alanmimms/NexRx/hw/DFM-fail.md

[C2862740, C133940, C133940, C133940, C133940, C133940, C1710,
C133940, C133940, C50254, C133940, C50254, C1710, C50254, C96446,
C1710, C913830, C1974049, C96446, C2862740, C96446, C96446, C96446,
C96446, C96446, C96446, C96446, C96446, C96446, C96446, C96446,
C76991, C96446, C96446, C96446, C96446, C96446, C96446, C96446,
C76991, C96446, C96446, C96446, C96446, C96446, C96446, C96446,
C96446, C52259879, C96446, C96446, C76991, C76991, C96446, C96446,
C96446, C52259879, C96446, C96446, C96446, C96446, C96446, C96446,
C96446, C96446, C96446, C96446, C96446, C96446, C96446, C96446,
C96446, C96446, C96446, C96446, C96446, C96446, C96446, C96446,
C96446] Pls replace the problem compoments to proceed as checked.
Please edit in 1427:54:8 hours, or else the order will be cancelled
automatically

As shown below, seems the packages of the parts ( U1501、U1504、
C133940, C1516、C1515、C1513、C1512、C219、C918、C1514、D101、C1517、
C1502、C1507、C1506、C207、C1006、C1004、C909、C1206、C911、C902、
C1005、C1511、C1009、C904、C208、C1003、C107、C1205、C108、C1008、
C1007、C1202、C922、C1201、C1204、C1203、C212、C937、C231、C228、C1501、
C903、C1404、C1406、C1409、C229、C218、C822、C943、C232、C1405、C1408、
C837、C944、C213、C1407、C1403、C227、C809、C844、C843、C230、C233、
C803、C811、C802、C804、C818、L304、L303、D201) cannot match the
corresponding footprint on the PCB board.

x C1003
x C1004
x C1005
x C1006
x C1007
x C1008
x C1009
x C108
x C1201
x C1202
x C1203
x C1204
x C1205
x C1206
x C1403
x C1404
x C1405
x C1406
x C1407
x C1408
x C1409
x C1501
x C1502
x C1506
x C1507
x C1511
x C1514
x C1517
x C207
x C208
x C212
x C213
x C218
x C227
x C228
x C229
x C230
x C231
x C232
x C233
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
