alanmimms/NexRx/CPLD/top.sv

import CPLDRegs::*;

/**
 * nexrx-top.sv
 * Top-level module for NexRx CPLDs.
 */
module top (
	    input  logic clkTCXO,	// External TCXO
	    input  logic clkSynth,	// Si5351 generated "VFO" for phase outputs

	    /* SPI Slave Interface */
	    input  logic spiSCK,
	    input  logic spiMOSI,
	    output logic spiMISO,
	    input  logic spiNSS,

	    input  logic gnssPPS,	// GNSS 1pps signal for TCXO freq counter

	    // Output for each octature phase
	    output logic [7:0] nPh
	    );

  timeunit 1ns;
  timeprecision 1ps;

  /* Clocking & Reset */
  logic clkSys;    // TCXO based Master Clock
  logic clkVFO;	   // Current "VFO" freq clock
  logic resetN;

  // THIS PROBABLY NEEDS GLOBAL CLOCK BUFFER.
  assign clkSys = clkTCXO;
  assign clkVFO = clkSynth;

  initial resetN = 1;
  initial control = initCPLDControl;

  //==================================================================
  // Register Bank & SPI
  //==================================================================
  tCPLDControl control;
  logic [63:0] tcxoValue;

  logic [31:0] shiftReg;
  logic [5:0]  bitCnt;
  logic [7:0]  cmdLatch;
  logic        cmdDone;

  logic [6:0]  addr;
  logic        isWrite;
  logic [31:0] dataIn;
  logic [31:0] dataOut;

  //==================================================================
  // SPI Frontend
  //==================================================================
  always_ff @(posedge spiSCK or posedge spiNSS) begin

    if (spiNSS) begin
      bitCnt <= 6'd0;
      cmdDone <= 1'b0;
      cmdLatch <= 8'h0;
    end else begin

      if (bitCnt < 6'd8) begin
        cmdLatch <= {cmdLatch[6:0], spiMOSI};
      end else begin
        shiftReg <= {shiftReg[30:0], spiMOSI};
      end

      if (bitCnt == 6'd39) begin
        cmdDone <= 1'b1;
      end else begin
        bitCnt <= bitCnt + 1'b1;
      end
    end
  end

  always_ff @(negedge spiSCK or posedge spiNSS) begin

    if (spiNSS) begin
      spiMISO <= 1'b0;
    end else begin

      if (bitCnt >= 6'd8 && bitCnt < 6'd40) begin
        spiMISO <= dataOut[39 - bitCnt];
      end else begin
        spiMISO <= 1'b0;
      end
    end
  end

  assign addr = cmdLatch[6:0];
  assign isWrite = cmdLatch[7];
  assign dataIn = shiftReg;

  //==================================================================
  // Register Logic
  //==================================================================
  always_ff @(posedge clkSys) begin

    if (cmdDone) begin

      if (isWrite) begin

        case (addr)
	  aCPLDControl:	control <= dataIn;
	  default: ;
        endcase
      end
    end
  end

  always_comb begin
    case (addr)
      aCPLDControl:	dataOut = 32'(control);
      aCPLDPPSLatchHi:	dataOut = tcxoValue[63:32];
      aCPLDPPSLatchLo:	dataOut = tcxoValue[31:0];
      aCPLDSig:		dataOut = eSigValVal;	/* 'NxRx' */
      default:		dataOut = 'hDEADBEEF;
    endcase
  end

  //==================================================================
  // Precision frequency counter for clkSys gated by 1pps from GNSS.
  //==================================================================
  logic [63:0] tcxoCounter;
  initial tcxoCounter = 0;

  // Synchronizer to bring 1pps signal into TCXO clock domain safely.
  logic [2:0] ppsSync;
  wire ppsRise = ppsSync[1] & ~ppsSync[2];

  always_ff @(posedge clkSys) begin
    ppsSync <= {ppsSync[1:0], gnssPPS};
  end

  always_ff @(posedge clkSys) begin
    tcxoCounter <= tcxoCounter + 1'b1;

    if (ppsRise) begin
      tcxoValue <= tcxoCounter;
    end
  end

  //==================================================================
  // Phase Generators (Walking Rings)
  //==================================================================
  logic [7:0] osdPhases;

  initial osdPhases = 8'b10000000;

  always_ff @(negedge clkVFO) begin

    if (control.octMode)
      nPh <= ~osdPhases;
    else
      nPh <= ~{'0, osdPhases[6], '0, osdPhases[4], '0, osdPhases[2], '0, osdPhases[0]};

    osdPhases <= {osdPhases[6:0], osdPhases[7]};
  end

endmodule
