alanmimms/NexRx/app/src/TwinConn.cpp

#include "TwinConn.hpp"
#include <cbor.h>
#include <iostream>
#include <cmath>

namespace nexrx {

TwinConn::~TwinConn() {
  shutdown();
}

bool TwinConn::initialize(const TwinConfig& cfg) {
  if (connected) {
    return true;
  }
  config = cfg;
  frameBuffer.reserve(cfg.frameBufferSize);

  TCPControlClientConfig controlConfig;
  controlConfig.host = cfg.host;
  controlConfig.port = cfg.controlPort;
  control = std::make_unique<TCPControlClient>(controlConfig);
  if (!control->connect()) {
    return false;
  }

  UDPStreamClientConfig streamConfig;
  streamConfig.port = cfg.streamPort;
  streamConfig.receiveBufferSize = cfg.receiveBufferSize;
  stream = std::make_unique<UDPStreamClient>(streamConfig);
  if (!stream->connect()) {
    return false;
  }

  connected = true;
  return true;
}

void TwinConn::shutdown() {
  stopReceiving();
  if (control && connected) {
    uint8_t buf[64];
    CborEncoder enc, arr;
    cbor_encoder_init(&enc, buf, sizeof(buf), 0);
    cbor_encoder_create_array(&enc, &arr, 1);
    cbor_encode_uint(&arr, Control::CMD_GBYE);
    cbor_encoder_close_container(&enc, &arr);
    sendCBORRequest(Control::CMD_GBYE, {buf, buf + cbor_encoder_get_buffer_size(&enc, buf)});
    control->disconnect();
  }
  if (stream) {
    stream->disconnect();
  }
  connected = false;
}

bool TwinConn::startReceiving() {
  if (!connected) {
    return false;
  }
  if (receiving) {
    return true;
  }
  stopRequested = false;
  receiving = true;
  receiveThread = std::thread(&TwinConn::receiveLoop, this);
  return true;
}

void TwinConn::stopReceiving() {
  if (!receiving) {
    return;
  }
  stopRequested = true;
  if (receiveThread.joinable()) {
    receiveThread.join();
  }
  receiving = false;
}

size_t TwinConn::pollFrames(size_t maxFrames) {
  if (!connected || !stream) {
    return 0;
  }
  frameBuffer.clear();
  size_t count = 0;
  while (count < maxFrames) {
    auto res = stream->read(std::chrono::milliseconds(0));
    if (!res.ok()) {
      break;
    }
    
    IQFrame frame = res.value;
    lastSequenceReceived = frame.sequence;
    lastFrameReceived = frame;
    ++framesReceivedCount;
    ++count;
    frameBuffer.push_back(frame);
  }

  if (count > 0) {
    std::lock_guard<std::mutex> lock(callbackMutex);
    if (frameCallback) {
      for (const auto& frame : frameBuffer) {
        frameCallback(frame);
      }
    }
    if (batchCallback) {
      batchCallback(frameBuffer);
    }
  }
  return count;
}

void TwinConn::receiveLoop() {
  while (!stopRequested) {
    if (pollFrames(2048) == 0) {
      std::this_thread::sleep_for(std::chrono::microseconds(100));
    }
  }
}

void TwinConn::pollStateAsync() {
  uint8_t buf[64];
  CborEncoder enc, arr;
  cbor_encoder_init(&enc, buf, sizeof(buf), 0);
  cbor_encoder_create_array(&enc, &arr, 1);
  cbor_encode_uint(&arr, Control::CMD_GET_STATE);
  cbor_encoder_close_container(&enc, &arr);
  
  auto resp = sendCBORRequest(Control::CMD_GET_STATE, {buf, buf + cbor_encoder_get_buffer_size(&enc, buf)});
  if (!resp.empty()) {
      std::lock_guard<std::mutex> lock(stateMutex);
      cachedStateCBOR = resp;
  }
}

std::vector<uint8_t> TwinConn::processResponse(const std::vector<uint8_t>& data, uint32_t cmdId) {
  (void)cmdId;
  if (data.empty()) {
    return {};
  }
  CborParser parser;
  CborValue it, array;
  if (cbor_parser_init(data.data(), data.size(), 0, &parser, &it) != CborNoError) {
    return {};
  }
  cbor_value_enter_container(&it, &array);
  int64_t status;
  cbor_value_get_int64(&array, &status);
  if (status != 0) {
    return {};
  }
  return data;
}

std::vector<uint8_t> TwinConn::sendCBORRequest(uint32_t cmdId, const std::vector<uint8_t>& request) {
  std::lock_guard<std::mutex> lock(controlMutex);
  auto res = control->sendRequest(request, std::chrono::milliseconds(500));
  if (!res.ok()) {
    return {};
  }
  return processResponse(res.value, cmdId);
}

bool TwinConn::setVFO(double freqHz, double offsetHz) {
  uint8_t buf[128];
  CborEncoder enc, arr;
  cbor_encoder_init(&enc, buf, sizeof(buf), 0);
  cbor_encoder_create_array(&enc, &arr, 3);
  cbor_encode_uint(&arr, Control::CMD_SET_VFO);
  cbor_encode_double(&arr, freqHz);
  cbor_encode_double(&arr, offsetHz);
  cbor_encoder_close_container(&enc, &arr);
  return !sendCBORRequest(Control::CMD_SET_VFO, {buf, buf + cbor_encoder_get_buffer_size(&enc, buf)}).empty();
}

bool TwinConn::setAtten(int dbValue) {
  uint8_t buf[128];
  CborEncoder enc, arr;
  cbor_encoder_init(&enc, buf, sizeof(buf), 0);
  cbor_encoder_create_array(&enc, &arr, 2);
  cbor_encode_uint(&arr, Control::CMD_SET_ATTEN);
  cbor_encode_int(&arr, dbValue);
  cbor_encoder_close_container(&enc, &arr);
  return !sendCBORRequest(Control::CMD_SET_ATTEN, {buf, buf + cbor_encoder_get_buffer_size(&enc, buf)}).empty();
}

bool TwinConn::setPGAGain(int code) {
  uint8_t buf[128];
  CborEncoder enc, arr;
  cbor_encoder_init(&enc, buf, sizeof(buf), 0);
  cbor_encoder_create_array(&enc, &arr, 2);
  cbor_encode_uint(&arr, Control::CMD_SET_PGA_GAIN);
  cbor_encode_int(&arr, code);
  cbor_encoder_close_container(&enc, &arr);
  return !sendCBORRequest(Control::CMD_SET_PGA_GAIN, {buf, buf + cbor_encoder_get_buffer_size(&enc, buf)}).empty();
}

bool TwinConn::setAGCMode(int mode) {
  uint8_t buf[128];
  CborEncoder enc, arr;
  cbor_encoder_init(&enc, buf, sizeof(buf), 0);
  cbor_encoder_create_array(&enc, &arr, 2);
  cbor_encode_uint(&arr, Control::CMD_SET_AGC_MODE);
  cbor_encode_int(&arr, mode);
  cbor_encoder_close_container(&enc, &arr);
  return !sendCBORRequest(Control::CMD_SET_AGC_MODE, {buf, buf + cbor_encoder_get_buffer_size(&enc, buf)}).empty();
}

bool TwinConn::setISGFreq(double freqHz) {
  uint8_t buf[128];
  CborEncoder enc, arr;
  cbor_encoder_init(&enc, buf, sizeof(buf), 0);
  cbor_encoder_create_array(&enc, &arr, 2);
  cbor_encode_uint(&arr, Control::CMD_SET_ISG_FREQ);
  cbor_encode_double(&arr, freqHz);
  cbor_encoder_close_container(&enc, &arr);
  return !sendCBORRequest(Control::CMD_SET_ISG_FREQ, {buf, buf + cbor_encoder_get_buffer_size(&enc, buf)}).empty();
}

bool TwinConn::setISGEnable(bool enabled) {
  uint8_t buf[64];
  CborEncoder enc, arr;
  cbor_encoder_init(&enc, buf, sizeof(buf), 0);
  cbor_encoder_create_array(&enc, &arr, 2);
  cbor_encode_uint(&arr, Control::CMD_SET_ISG_ENABLE);
  cbor_encode_boolean(&arr, enabled);
  cbor_encoder_close_container(&enc, &arr);
  return !sendCBORRequest(Control::CMD_SET_ISG_ENABLE, {buf, buf + cbor_encoder_get_buffer_size(&enc, buf)}).empty();
}

bool TwinConn::setHpfBypass(bool bypass) {
  uint8_t buf[64];
  CborEncoder enc, arr;
  cbor_encoder_init(&enc, buf, sizeof(buf), 0);
  cbor_encoder_create_array(&enc, &arr, 2);
  cbor_encode_uint(&arr, Control::CMD_SET_HPF_BYPASS);
  cbor_encode_boolean(&arr, bypass);
  cbor_encoder_close_container(&enc, &arr);
  return !sendCBORRequest(Control::CMD_SET_HPF_BYPASS, {buf, buf + cbor_encoder_get_buffer_size(&enc, buf)}).empty();
}

bool TwinConn::setBpfIndex(int index) {
  uint8_t buf[64];
  CborEncoder enc, arr;
  cbor_encoder_init(&enc, buf, sizeof(buf), 0);
  cbor_encoder_create_array(&enc, &arr, 2);
  cbor_encode_uint(&arr, Control::CMD_SET_BPF_SELECT);
  cbor_encode_uint(&arr, (uint64_t)index);
  cbor_encoder_close_container(&enc, &arr);
  return !sendCBORRequest(Control::CMD_SET_BPF_SELECT, {buf, buf + cbor_encoder_get_buffer_size(&enc, buf)}).empty();
}

bool TwinConn::setTrMode(int mode) {
  uint8_t buf[128];
  CborEncoder enc, arr;
  cbor_encoder_init(&enc, buf, sizeof(buf), 0);
  cbor_encoder_create_array(&enc, &arr, 2);
  cbor_encode_uint(&arr, Control::CMD_SET_TR_MODE);
  cbor_encode_int(&arr, mode);
  cbor_encoder_close_container(&enc, &arr);
  return !sendCBORRequest(Control::CMD_SET_TR_MODE, {buf, buf + cbor_encoder_get_buffer_size(&enc, buf)}).empty();
}

bool TwinConn::setOSDOffsetKHz(double khz) {
  (void)khz;
  return true;
}

bool TwinConn::setQsdOffsetKHz(double khz) {
  return setOSDOffsetKHz(khz);
}

bool TwinConn::sendCalibrationStimulus(double freqHz, uint64_t durationMs) {
  uint8_t buf[128];
  CborEncoder enc, arr;
  cbor_encoder_init(&enc, buf, sizeof(buf), 0);
  cbor_encoder_create_array(&enc, &arr, 3);
  cbor_encode_uint(&arr, Control::CMD_CAL_STIM);
  cbor_encode_double(&arr, freqHz);
  cbor_encode_uint(&arr, durationMs);
  cbor_encoder_close_container(&enc, &arr);
  return !sendCBORRequest(Control::CMD_CAL_STIM, {buf, buf + cbor_encoder_get_buffer_size(&enc, buf)}).empty();
}

bool TwinConn::startStream() {
  uint8_t buf[64];
  CborEncoder enc, arr;
  cbor_encoder_init(&enc, buf, sizeof(buf), 0);
  cbor_encoder_create_array(&enc, &arr, 1);
  cbor_encode_uint(&arr, Control::CMD_START_STREAM);
  cbor_encoder_close_container(&enc, &arr);
  return !sendCBORRequest(Control::CMD_START_STREAM, {buf, buf + cbor_encoder_get_buffer_size(&enc, buf)}).empty();
}

bool TwinConn::stopStream() {
  uint8_t buf[64];
  CborEncoder enc, arr;
  cbor_encoder_init(&enc, buf, sizeof(buf), 0);
  cbor_encoder_create_array(&enc, &arr, 1);
  cbor_encode_uint(&arr, Control::CMD_STOP_STREAM);
  cbor_encoder_close_container(&enc, &arr);
  return !sendCBORRequest(Control::CMD_STOP_STREAM, {buf, buf + cbor_encoder_get_buffer_size(&enc, buf)}).empty();
}

uint64_t TwinConn::getTimestamp() {
  uint8_t buf[64];
  CborEncoder enc, arr;
  cbor_encoder_init(&enc, buf, sizeof(buf), 0);
  cbor_encoder_create_array(&enc, &arr, 1);
  cbor_encode_uint(&arr, Control::CMD_GET_TIMESTAMP);
  cbor_encoder_close_container(&enc, &arr);
  auto res = sendCBORRequest(Control::CMD_GET_TIMESTAMP, {buf, buf + cbor_encoder_get_buffer_size(&enc, buf)});
  if (res.empty()) {
    return 0;
  }
  return 0; // TODO: Implement CBOR decode
}

TwinConn::VersionInfo TwinConn::checkFirmwareVersion() {
  VersionInfo info;
  uint8_t buf[64];
  CborEncoder enc, arr;
  cbor_encoder_init(&enc, buf, sizeof(buf), 0);
  cbor_encoder_create_array(&enc, &arr, 1);
  cbor_encode_uint(&arr, Control::CMD_GET_VERSION);
  cbor_encoder_close_container(&enc, &arr);

  auto res = sendCBORRequest(Control::CMD_GET_VERSION, {buf, buf + cbor_encoder_get_buffer_size(&enc, buf)});
  if (res.empty()) {
    return info;
  }

  CborParser parser;
  CborValue it;
  if (cbor_parser_init(res.data(), res.size(), 0, &parser, &it) != CborNoError) {
    return info;
  }

  if (cbor_value_is_array(&it)) {
    CborValue val;
    cbor_value_enter_container(&it, &val);

    int64_t status = -1;
    if (cbor_value_is_integer(&val)) {
      cbor_value_get_int64(&val, &status);
      cbor_value_advance(&val);
    }
    if (status != 0) {
      return info;
    }

    uint64_t magic = 0, major = 0, minor = 0, patch = 0, hwState = 0;
    if (cbor_value_is_integer(&val)) { cbor_value_get_uint64(&val, &magic); cbor_value_advance(&val); }
    if (cbor_value_is_integer(&val)) { cbor_value_get_uint64(&val, &major); cbor_value_advance(&val); }
    if (cbor_value_is_integer(&val)) { cbor_value_get_uint64(&val, &minor); cbor_value_advance(&val); }
    if (cbor_value_is_integer(&val)) { cbor_value_get_uint64(&val, &patch); cbor_value_advance(&val); }
    if (cbor_value_is_integer(&val)) { cbor_value_get_uint64(&val, &hwState); cbor_value_advance(&val); }

    info.magic = static_cast<uint32_t>(magic);
    info.major = static_cast<uint16_t>(major);
    info.minor = static_cast<uint16_t>(minor);
    info.patch = static_cast<uint16_t>(patch);
    info.hwState = static_cast<uint32_t>(hwState);
    info.valid = true;
    info.compatible = (info.magic == Control::FW_PROTOCOL_MAGIC && info.major == Control::FW_VERSION_MAJOR);
  }

  return info;
}

bool TwinConn::loadCPLDBitstream(const std::vector<uint8_t>& bitstream) {
  if (bitstream.empty()) {
    return false;
  }
  std::vector<uint8_t> buf;
  buf.resize(bitstream.size() + 64);

  CborEncoder enc, arr;
  cbor_encoder_init(&enc, buf.data(), buf.size(), 0);
  cbor_encoder_create_array(&enc, &arr, 2);
  cbor_encode_uint(&arr, Control::CMD_LOAD_CPLD);
  cbor_encode_byte_string(&arr, bitstream.data(), bitstream.size());
  cbor_encoder_close_container(&enc, &arr);

  size_t encodedLen = cbor_encoder_get_buffer_size(&enc, buf.data());
  auto res = sendCBORRequest(Control::CMD_LOAD_CPLD, {buf.data(), buf.data() + encodedLen});
  if (res.empty()) {
    return false;
  }

  CborParser parser;
  CborValue it;
  if (cbor_parser_init(res.data(), res.size(), 0, &parser, &it) != CborNoError) {
    return false;
  }

  if (cbor_value_is_array(&it)) {
    CborValue val;
    cbor_value_enter_container(&it, &val);
    int64_t status = -1;
    if (cbor_value_is_integer(&val)) {
      cbor_value_get_int64(&val, &status);
    }
    return (status == 0);
  }

  return false;
}

std::vector<uint8_t> TwinConn::getState() {
  std::lock_guard<std::mutex> lock(stateMutex);
  return cachedStateCBOR;
}

uint64_t TwinConn::getPacketsReceived() const {
  return stream ? stream->packetsReceived() : 0;
}

uint64_t TwinConn::getBufferOverruns() const {
  return stream ? stream->bufferOverruns() : 0;
}

uint64_t TwinConn::getFramesDropped() const {
  return stream ? stream->framesDropped() : 0;
}

} // namespace nexrx
