alanmimms/NexRx/app/src/GUIEngine.cpp

#include "GUIEngine.hpp"
#include "AppLuaBridge.hpp"
#include <iostream>
#include <iomanip>
#include <fstream>
#include <csignal>
#include <cbor.h>

GUIEngine::GUIEngine(DSPEngine& dsp) : dsp_(dsp) {}

GUIEngine::~GUIEngine() {
  shutdown();
}

bool GUIEngine::init(const std::string& title, bool vsyncEnabled) {
  // 1. Raylib Setup
  SetConfigFlags(FLAG_WINDOW_RESIZABLE | (vsyncEnabled ? FLAG_VSYNC_HINT : 0));
  InitWindow(1280, 850, title.c_str());
  SetTargetFPS(60);

  // 2. Load Font
  Font font = LoadFontEx("fonts/DejaVuSans.ttf", 32, NULL, 0);
  if (font.texture.id == 0) font = LoadFontEx("app/fonts/DejaVuSans.ttf", 32, NULL, 0);
  if (font.texture.id == 0) font = LoadFontEx("../fonts/DejaVuSans.ttf", 32, NULL, 0);
  if (font.texture.id == 0) font = LoadFontEx("uitest/fonts/DejaVuSans.ttf", 32, NULL, 0);
  if (font.texture.id == 0) font = LoadFontEx("../uitest/fonts/DejaVuSans.ttf", 32, NULL, 0);
  
  if (font.texture.id != 0) {
    SetTextureFilter(font.texture, TEXTURE_FILTER_BILINEAR);
    AppLuaBridge::setFont(font);
  }

  // 3. Audio & Waterfall init
  if (!audio.init(48000, 2)) return false;
  if (!waterfall.init(DSPEngine::FFT_SIZE, 256)) return false;

  // Configure audio buffer for smooth jitter absorption with 50ms batches
  BufferConfig audioConfig;
  audioConfig.capacity = 32768;
  audioConfig.targetFillRatio = 0.35f;
  audioConfig.lowThreshold = 0.15f;
  audioConfig.highThreshold = 0.65f;
  audioConfig.enableAdaptation = true;
  dsp_.getAudioBuffer().configure(audioConfig);

  audio.setCallback([this](float* out, uint32_t fC, uint32_t ch) {
    thread_local std::vector<float> tmp;
    tmp.resize(fC);
    size_t read = dsp_.getAudioBuffer().read(std::span<float>(tmp.data(), fC));
    for (uint32_t i = 0; i < fC; ++i) {
      float s = (i < read) ? tmp[i] : 0.0f;
      for (uint32_t c = 0; c < ch; ++c) out[i*ch + c] = s;
    }
  });

  // 4. Lua Setup
  std::string prefix = "";
  if (!std::ifstream("lua/SetBox.lua").good() && std::ifstream("app/lua/SetBox.lua").good()) {
    prefix = "app/";
  }

  lua.open_libraries(sol::lib::base, sol::lib::package, sol::lib::table, sol::lib::string, sol::lib::math, sol::lib::os, sol::lib::debug, sol::lib::io);
  lua["appPrefix"] = prefix;
  lua["basePath"] = prefix + "lua/";
  std::string pkgPath = prefix + "lua/?.lua;" + prefix + "lua/?/init.lua;" + prefix + "?.lua;" + prefix + "?/init.lua;lua/?.lua;lua/?/init.lua";
  lua["package"]["path"] = pkgPath;
  
  AppLuaBridge::registerWithLua(lua, this);

  try {
    // Load SetBox first as it's a core dependency
    lua.safe_script_file(prefix + "lua/SetBox.lua");
    
    // Load the main entry point
    lua.safe_script_file(prefix + "lua/Main.lua");
    
    // In our new architecture, Main.lua should return the UI module with standard hooks
    uiModule = lua["UI"]; 
  } catch (const sol::error& e) {
    std::cerr << "Lua load error: " << e.what() << std::endl;
    return false;
  }

  // 5. App Initialization
  sol::protected_function initFn = lua["init"];
  if (initFn.valid()) {
    auto res = initFn();
    if (!res.valid()) { sol::error err = res; std::cerr << "Lua init() error: " << err.what() << std::endl; return false; }
  }

  startCommandThread();
  running = true;
  return true;
}

extern std::atomic<bool> gRunning;

void GUIEngine::run() {
  while (running && !WindowShouldClose() && gRunning.load()) {
    float dt = GetFrameTime();
    update(dt);
    render();
  }
}

void GUIEngine::update(float dt) {
  // 1. Poll input and dispatch to Lua UI if needed
  if (uiModule != sol::nil) {
    Vector2 mousePos = GetMousePosition();
    
    // Mouse Buttons & Wheel
    sol::function onMouseEvent = uiModule["onMouseEvent"];
    if (onMouseEvent.valid()) {
        int mods = 0;
        if (IsKeyDown(KEY_LEFT_SHIFT) || IsKeyDown(KEY_RIGHT_SHIFT)) mods |= 1;
        if (IsKeyDown(KEY_LEFT_CONTROL) || IsKeyDown(KEY_RIGHT_CONTROL)) mods |= 2;
        if (IsKeyDown(KEY_LEFT_ALT) || IsKeyDown(KEY_RIGHT_ALT)) mods |= 4;

        // Motion dispatch (ensure mouse coordinates are updated)
        onMouseEvent("motion", mousePos.x, mousePos.y, 0, false, mods);

        for (int b = 0; b < 3; b++) {
            if (IsMouseButtonPressed(b)) onMouseEvent("button", mousePos.x, mousePos.y, b, true, mods);
            else if (IsMouseButtonReleased(b)) onMouseEvent("button", mousePos.x, mousePos.y, b, false, mods);
        }

        // Mouse Wheel
        float wheel = GetMouseWheelMove();
        if (wheel != 0) onMouseEvent("wheel", mousePos.x, mousePos.y, (int)wheel, false, mods);
    }

    // Keys (Simplified: Raylib doesn't have a clean event queue for releases/repeats without more work)
    sol::function onKeyEvent = uiModule["onKeyEvent"];
    if (onKeyEvent.valid()) {
        // Handle character input (digits, letters, etc)
        int charCode = GetCharPressed();
        while (charCode > 0) {
            sol::function onTextInput = uiModule["onTextInput"];
            if (onTextInput.valid()) {
                char text[2] = {(char)charCode, 0};
                onTextInput(text);
            }
            charCode = GetCharPressed();
        }

        // Handle special keys (Arrow keys, ENTER, BACKSPACE, ESC)
        int keys[] = {KEY_RIGHT, KEY_LEFT, KEY_UP, KEY_DOWN, KEY_ENTER, KEY_BACKSPACE, KEY_ESCAPE, KEY_F};
        for (int k : keys) {
            if (IsKeyPressed(k)) {
                // std::cout << "[C++] Key Pressed: " << k << std::endl;
                onKeyEvent(k, true, 0);
            }
            else if (IsKeyReleased(k)) {
                onKeyEvent(k, false, 0);
            }
        }
    }
  }

  // 2. Lua update hook
  sol::protected_function updateFn = lua["update"];
  if (updateFn.valid()) { 
    auto res = updateFn(dt); 
    if (!res.valid()) { sol::error err = res; std::cerr << "Lua update() error: " << err.what() << std::endl; running = false; } 
  }

  // 3. Periodic 1-second diagnostics (Stages C & D)
  statTimer += dt;
  if (statTimer >= 1.0f) {
    statTimer -= 1.0f;
    uint64_t curPkts = twinHost.getPacketsReceived();
    uint64_t curFrames = twinHost.getFramesReceived();
    uint64_t curNetDropped = twinHost.getFramesDropped();
    uint64_t curOverruns = twinHost.getBufferOverruns();
    uint64_t curDspFrames = dsp_.getDiagnostics().framesProcessed.load();
    const auto& aStats = dsp_.getAudioBuffer().stats();
    uint64_t curAudioWritten = aStats.samplesWritten.load();
    uint64_t curAudioRead = aStats.samplesRead.load();
    uint64_t curAudioDrops = aStats.dropsOverflow.load();
    uint64_t curAudioUnderruns = aStats.underruns.load();
    uint64_t curAudioStretch = aStats.stretchCount.load();
    float fillPct = dsp_.getAudioBuffer().getFillRatio() * 100.0f;

    float ingestKsps = static_cast<float>(curFrames - lastStatFrames) / 1000.0f;
    float pktsPerSec = static_cast<float>(curPkts - lastStatPkts);
    uint64_t netDroppedDelta = curNetDropped - lastStatNetDropped;
    uint64_t overrunsDelta = curOverruns - lastStatOverruns;
    float dspKsps = static_cast<float>(curDspFrames - lastStatDspFrames) / 1000.0f;
    float audioGenRate = static_cast<float>(curAudioWritten - lastStatAudioWritten);
    float audioPlayRate = static_cast<float>(curAudioRead - lastStatAudioRead);
    uint64_t audioDropsDelta = curAudioDrops - lastStatAudioDrops;
    uint64_t audioUnderrunsDelta = curAudioUnderruns - lastStatAudioUnderruns;
    uint64_t audioStretchDelta = curAudioStretch - lastStatAudioStretch;

    lastStatPkts = curPkts;
    lastStatFrames = curFrames;
    lastStatNetDropped = curNetDropped;
    lastStatOverruns = curOverruns;
    lastStatDspFrames = curDspFrames;
    lastStatAudioWritten = curAudioWritten;
    lastStatAudioRead = curAudioRead;
    lastStatAudioDrops = curAudioDrops;
    lastStatAudioUnderruns = curAudioUnderruns;
    lastStatAudioStretch = curAudioStretch;

    if (twinConnected.load()) {
      std::cout << "[App Stats 1s] Stage C Ingest: " << std::fixed << std::setprecision(1) << ingestKsps 
                << " ksps (" << std::setprecision(0) << pktsPerSec << " pkts/s) | Net Lost: "
                << netDroppedDelta << " (total " << curNetDropped << ") | Overruns: " 
                << overrunsDelta << " (total " << curOverruns << ") | Stage D DSP: " 
                << std::setprecision(1) << dspKsps << " ksps -> Audio Gen: " 
                << std::setprecision(0) << audioGenRate << " s/s | Playback: " << audioPlayRate 
                << " s/s (fill " << std::setprecision(1) << fillPct << "%, drops " 
                << audioDropsDelta << ", underruns " << audioUnderrunsDelta 
                << ", stretch " << audioStretchDelta << ")" << std::endl;
    }
  }
}

void GUIEngine::render() {
  if (IsWindowResized() && uiModule != sol::nil) {
    sol::function resizeFunc = uiModule["onResize"];
    if (resizeFunc.valid()) resizeFunc(GetScreenWidth(), GetScreenHeight());
  }

  BeginDrawing();
  ClearBackground(BLACK);

  if (uiModule != sol::nil) {
    sol::function renderFunc = uiModule["render"];
    if (renderFunc.valid()) {
      try {
        renderFunc(GetScreenWidth(), GetScreenHeight());
      } catch (const sol::error& e) {
        std::cerr << "Lua render error: " << e.what() << std::endl;
      }
    }
  }

  if (firmwareIncompatible) {
    renderIncompatibleFirmwareModal();
  }

  EndDrawing();
}

void GUIEngine::renderIncompatibleFirmwareModal() {
  int screenW = GetScreenWidth();
  int screenH = GetScreenHeight();

  // Dark overlay
  DrawRectangle(0, 0, screenW, screenH, Fade(BLACK, 0.80f));

  // Modal box
  int boxW = 540;
  int boxH = 260;
  int boxX = (screenW - boxW) / 2;
  int boxY = (screenH - boxH) / 2;

  DrawRectangle(boxX, boxY, boxW, boxH, Color{30, 32, 38, 255});
  DrawRectangleLines(boxX, boxY, boxW, boxH, Color{220, 50, 50, 255});
  DrawRectangleLines(boxX + 1, boxY + 1, boxW - 2, boxH - 2, Color{220, 50, 50, 180});

  // Header banner
  DrawRectangle(boxX + 2, boxY + 2, boxW - 4, 38, Color{180, 30, 30, 255});
  DrawText("FIRMWARE UPDATE REQUIRED", boxX + 20, boxY + 10, 20, WHITE);

  // Body text
  char verLine[128];
  snprintf(verLine, sizeof(verLine), "Connected Hardware: Firmware v%u.%u.%u",
           connectedVersion.major, connectedVersion.minor, connectedVersion.patch);
  DrawText(verLine, boxX + 25, boxY + 55, 18, Color{220, 220, 220, 255});

  char reqLine[128];
  snprintf(reqLine, sizeof(reqLine), "Application Requires: Firmware v%u.%u.x",
           nexrx::Control::FW_VERSION_MAJOR, nexrx::Control::FW_VERSION_MINOR);
  DrawText(reqLine, boxX + 25, boxY + 80, 18, Color{255, 200, 80, 255});

  DrawText("ATTENTION: Continuing without updating will prevent NexRx", boxX + 25, boxY + 115, 16, Color{255, 120, 120, 255});
  DrawText("from operating. The receiver hardware cannot communicate", boxX + 25, boxY + 135, 16, Color{255, 120, 120, 255});
  DrawText("with this version of the application.", boxX + 25, boxY + 155, 16, Color{255, 120, 120, 255});

  // Buttons
  Rectangle updateBtn = { static_cast<float>(boxX + 30), static_cast<float>(boxY + 195), 230, 42 };
  Rectangle cancelBtn = { static_cast<float>(boxX + 280), static_cast<float>(boxY + 195), 230, 42 };

  Vector2 mousePos = GetMousePosition();
  bool hoverUpdate = CheckCollisionPointRec(mousePos, updateBtn);
  bool hoverCancel = CheckCollisionPointRec(mousePos, cancelBtn);

  // Draw Update Button
  DrawRectangleRec(updateBtn, hoverUpdate ? Color{40, 160, 60, 255} : Color{30, 130, 50, 255});
  DrawRectangleLinesEx(updateBtn, 1.5f, Color{80, 220, 100, 255});
  DrawText("Update Firmware Now", boxX + 48, boxY + 207, 18, WHITE);

  // Draw Cancel Button
  DrawRectangleRec(cancelBtn, hoverCancel ? Color{100, 100, 110, 255} : Color{70, 70, 80, 255});
  DrawRectangleLinesEx(cancelBtn, 1.5f, Color{150, 150, 160, 255});
  DrawText("Disconnect / Cancel", boxX + 308, boxY + 207, 18, WHITE);

  // Handle clicks
  if (IsMouseButtonPressed(MOUSE_BUTTON_LEFT)) {
    if (hoverUpdate) {
      std::cout << "[Hardware] User initiated firmware update..." << std::endl;
      firmwareIncompatible = false;
    } else if (hoverCancel) {
      std::cout << "[Hardware] User declined firmware update. Hardware remaining disconnected." << std::endl;
      firmwareIncompatible = false;
    }
  }
}

void GUIEngine::shutdown() {
  running = false;
  stopCommandThread();
  twinHost.shutdown();
  audio.shutdown();
  waterfall.shutdown();
  CloseWindow();
}

bool GUIEngine::connectTwin(const std::string& host, int cp, int sp) {
  nexrx::TwinConfig c; c.host = host; c.controlPort = cp; c.streamPort = sp;
  if (twinHost.initialize(c)) {
    auto vInfo = twinHost.checkFirmwareVersion();
    if (vInfo.valid) {
      connectedVersion = vInfo;
      if (!vInfo.compatible) {
        std::cerr << "[Hardware] Connected firmware v" << vInfo.major << "." << vInfo.minor << "." << vInfo.patch
                  << " is INCOMPATIBLE with App required v" << nexrx::Control::FW_VERSION_MAJOR << "."
                  << nexrx::Control::FW_VERSION_MINOR << "!" << std::endl;
        firmwareIncompatible = true;
        twinHost.shutdown();
        twinConnected.store(false);
        return false;
      }
      firmwareIncompatible = false;

      if (vInfo.hwState == nexrx::Control::STATE_WAIT_CPLD_IMAGE) {
        std::ifstream bitstreamFile("common/cpld.bin", std::ios::binary);
        if (!bitstreamFile.is_open()) {
          bitstreamFile.open("app/assets/cpld.bin", std::ios::binary);
        }
        if (bitstreamFile.is_open()) {
          std::vector<uint8_t> bitstreamData((std::istreambuf_iterator<char>(bitstreamFile)),
                                             std::istreambuf_iterator<char>());
          std::cout << "[Hardware] Pushing CPLD bitstream (" << bitstreamData.size() << " bytes) to hardware..." << std::endl;
          twinHost.loadCPLDBitstream(bitstreamData);
        } else {
          std::cerr << "[Hardware] Warning: CPLD bitstream file not found on host!" << std::endl;
        }
      }
    }

    twinHost.setFrameCallback([this](const nexrx::IQFrame& f) { dsp_.processIQFrame(f); });
    if (twinHost.startReceiving()) {
      twinConnected.store(true);
      twinHost.startStream();
      return true;
    }
  }
  return false;
}

void GUIEngine::disconnectTwin() {
  if (twinConnected.load()) {
    postTwinCommand("SHUTDOWN", [this]() { twinHost.stopReceiving(); twinHost.shutdown(); });
    twinConnected.store(false);
  }
}

sol::object GUIEngine::getTwinState(sol::this_state s) {
  if (!twinConnected.load()) return sol::make_object(s, sol::nil);
  
  auto now = std::chrono::steady_clock::now();
  if (now - lastStatePollTime > std::chrono::milliseconds(100)) {
    lastStatePollTime = now;
    postTwinCommand("POLL_STATE", [this](){ twinHost.pollStateAsync(); });
  }

  auto stateCBOR = twinHost.getState();
  if (stateCBOR.empty()) return sol::make_object(s, sol::nil);
  
  CborParser parser; CborValue it;
  if (cbor_parser_init(stateCBOR.data(), stateCBOR.size(), 0, &parser, &it) != CborNoError) return sol::make_object(s, sol::nil);
  
  sol::state_view lView(s); sol::table res = lView.create_table();
  CborValue mapIt;
  if (cbor_value_is_array(&it)) {
    CborValue arrayIt; cbor_value_enter_container(&it, &arrayIt); cbor_value_advance(&arrayIt);
    if (cbor_value_is_map(&arrayIt)) cbor_value_enter_container(&arrayIt, &mapIt);
    else return sol::make_object(s, sol::nil);
  } else if (cbor_value_is_map(&it)) cbor_value_enter_container(&it, &mapIt);
  else return sol::make_object(s, sol::nil);

  while (!cbor_value_at_end(&mapIt)) {
    char key[64]; size_t len = sizeof(key) - 1;
    if (cbor_value_get_type(&mapIt) == CborTextStringType) {
      if (cbor_value_copy_text_string(&mapIt, key, &len, &mapIt) != CborNoError) break;
      key[len] = '\0';
    } else { cbor_value_advance(&mapIt); continue; }
    if (cbor_value_at_end(&mapIt)) break;
    if (cbor_value_is_double(&mapIt)) { double v; cbor_value_get_double(&mapIt, &v); res[key] = v; }
    else if (cbor_value_is_integer(&mapIt)) { int64_t v; cbor_value_get_int64(&mapIt, &v); res[key] = v; }
    else if (cbor_value_is_boolean(&mapIt)) { bool v; cbor_value_get_boolean(&mapIt, &v); res[key] = v; }
    cbor_value_advance(&mapIt);
  }
  return res;
}

void GUIEngine::startCommandThread() {
  commandThreadRunning = true;
  commandThread = std::thread([this]() {
    while (commandThreadRunning) {
      std::function<void()> cmd;
      {
        std::lock_guard<std::mutex> l(cmdMutex);
        if (!pendingCommands.empty()) {
          auto it = pendingCommands.begin();
          cmd = it->second;
          pendingCommands.erase(it);
        }
      }
      if (cmd) {
        cmd();
      } else {
        std::this_thread::sleep_for(std::chrono::milliseconds(5));
      }
    }
  });
}

void GUIEngine::stopCommandThread() { commandThreadRunning = false; if (commandThread.joinable()) commandThread.join(); }

void GUIEngine::postTwinCommand(const std::string& name, std::function<void()> cmd) {
  std::lock_guard<std::mutex> l(cmdMutex);
  pendingCommands[name] = cmd;
}
