alanmimms/NexRx/twin/src/stimulus/StimulusLua.cpp

// NexRx Digital Twin - Stimulus Lua Bindings Implementation
//
// Copyright 2026 NexRx Project - MIT License

#include "StimulusLua.hpp"
#include "MorseGenerator.hpp"
#include "SSBGenerator.hpp"
#include "AMGenerator.hpp"
#include "SweepGenerator.hpp"
#include "TTSEngine.hpp"
#include "ToneGenerator.hpp"
#include "NoiseGenerator.hpp"

#include <cstring>
#include <iostream>
#include <fstream>

#include "RFCapturePlayer.hpp"

namespace nexrx {

StimulusLua::StimulusLua()
    : manager_(std::make_shared<StimulusManager>())
{}

StimulusLua::StimulusLua(std::shared_ptr<StimulusManager> manager)
    : manager_(std::move(manager))
{}

// Internal helper for WAV loading
static std::vector<float> loadWavFile(const std::string& path, uint32_t& outSampleRate) {
    std::string tryPaths[] = { path, "twin/" + path, "../" + path, "../../" + path };
    std::ifstream file;
    std::string foundPath;

    for (const auto& p : tryPaths) {
        file.open(p, std::ios::binary);
        if (file.is_open()) {
            foundPath = p;
            break;
        }
    }

    if (!file.is_open()) {
        std::cerr << "[Stimulus] Failed to open WAV file: " << path << " (checked common sub/parent dirs)" << std::endl;
        return {};
    }

    char header[44];
    file.read(header, 44);
    if (file.gcount() < 44) return {};

    if (std::strncmp(header, "RIFF", 4) != 0 || std::strncmp(header + 8, "WAVE", 4) != 0) {
        std::cerr << "[Stimulus] Invalid WAV header: " << foundPath << std::endl;
        return {};
    }

    // Basic WAV parsing
    uint16_t audioFormat = *reinterpret_cast<uint16_t*>(header + 20);
    uint16_t numChannels = *reinterpret_cast<uint16_t*>(header + 22);
    uint32_t sampleRate = *reinterpret_cast<uint32_t*>(header + 24);
    uint16_t bitsPerSample = *reinterpret_cast<uint16_t*>(header + 34);
    outSampleRate = sampleRate;

    // Skip to data chunk
    file.seekg(12);
    while (file.good()) {
        char chunkId[4];
        uint32_t chunkSize;
        file.read(chunkId, 4);
        file.read(reinterpret_cast<char*>(&chunkSize), 4);
        if (std::strncmp(chunkId, "data", 4) == 0) {
            size_t bytesPerSample = bitsPerSample / 8;
            size_t numSamples = chunkSize / bytesPerSample / numChannels;
            std::vector<float> samples(numSamples);
            
            for (size_t i = 0; i < numSamples; ++i) {
                float sample = 0.0f;
                if (audioFormat == 3 && bitsPerSample == 32) {
                    // IEEE Float
                    file.read(reinterpret_cast<char*>(&sample), 4);
                } else if (audioFormat == 1) {
                    // PCM Integer
                    if (bitsPerSample == 16) {
                        int16_t s; file.read(reinterpret_cast<char*>(&s), 2);
                        sample = s / 32768.0f;
                    } else if (bitsPerSample == 8) {
                        uint8_t s; file.read(reinterpret_cast<char*>(&s), 1);
                        sample = (s - 128) / 128.0f;
                    } else if (bitsPerSample == 24) {
                        uint8_t b[3]; file.read(reinterpret_cast<char*>(b), 3);
                        int32_t s = (b[0] << 8) | (b[1] << 16) | (b[2] << 24);
                        sample = (s >> 8) / 8388608.0f;
                    } else if (bitsPerSample == 32) {
                        int32_t s; file.read(reinterpret_cast<char*>(&s), 4);
                        sample = s / 2147483648.0f;
                    }
                }
                samples[i] = sample;
                // Skip extra channels
                if (numChannels > 1) {
                    file.seekg(bytesPerSample * (numChannels - 1), std::ios::cur);
                }
            }
            return samples;
        }
        file.seekg(chunkSize, std::ios::cur);
    }
    return {};
}

void StimulusLua::registerBindings(sol::state& lua) {
    // Create stimulus table
    sol::table stimulus = lua.create_named_table("stimulus");

    // stimulus.addMorse(name, config)
    stimulus["addMorse"] = [this](const std::string& name, sol::table config) {
        double freq = config.get_or("freq", 14.0e6);
        double amplitude = config.get_or("amplitude", 50e-6);  // ~S9 default
        std::string text = config.get_or<std::string>("text", "CQ");
        double wpm = config.get_or("wpm", 20.0);
        bool repeat = config.get_or("loop", true);

        auto morse = std::make_shared<MorseGenerator>(freq, amplitude, text, wpm);
        morse->setRepeat(repeat);

        manager_->addStimulus(name, morse, "morse", freq, amplitude);

        std::cout << "[Stimulus] Added Morse '" << name << "': "
                  << freq / 1e6 << " MHz, " << wpm << " WPM, \""
                  << text.substr(0, 20) << (text.size() > 20 ? "..." : "")
                  << "\"" << std::endl;
    };

    // stimulus.addSsb(name, config)
    stimulus["addSsb"] = [this](const std::string& name, sol::table config) {
        double freq = config.get_or("freq", 14.2e6);
        double amplitude = config.get_or("amplitude", 50e-6);
        std::string modeStr = config.get_or<std::string>("mode", "usb");

        SSBGenerator::Mode mode = (modeStr == "lsb" || modeStr == "LSB")
            ? SSBGenerator::Mode::LSB
            : SSBGenerator::Mode::USB;

        auto ssb = std::make_shared<SSBGenerator>(freq, amplitude, mode);

        // Check for tones
        sol::optional<sol::table> tonesOpt = config["tones"];
        if (tonesOpt) {
            std::vector<double> tones;
            for (auto& kv : *tonesOpt) {
                tones.push_back(kv.second.as<double>());
            }
            ssb->setTones(tones);

            manager_->addStimulus(name, ssb, "ssb", freq, amplitude);

            std::cout << "[Stimulus] Added SSB '" << name << "': "
                      << freq / 1e6 << " MHz " << modeStr << ", "
                      << tones.size() << " tone(s)" << std::endl;
            return;
        }

        // Check for voice (espeak-ng TTS)
        sol::optional<std::string> voiceOpt = config["voice"];
        if (voiceOpt) {
            bool repeat = config.get_or("loop", true);

            auto tts = std::make_shared<TTSEngine>();
            tts->setText(*voiceOpt);
            tts->setRepeat(repeat);

            // espeak-ng voice parameters
            if (auto v = config.get<sol::optional<std::string>>("voiceName")) {
                tts->setVoiceName(*v);
            }
            if (auto v = config.get<sol::optional<int>>("rate")) {
                tts->setRate(*v);
            }
            if (auto v = config.get<sol::optional<int>>("pitch")) {
                tts->setPitch(*v);
            }
            if (auto v = config.get<sol::optional<int>>("pitchRange")) {
                tts->setRange(*v);
            }
            if (auto v = config.get<sol::optional<int>>("volume")) {
                tts->setVolume(*v);
            }
            if (auto v = config.get<sol::optional<int>>("wordGap")) {
                tts->setWordGap(*v);
            }
            if (auto v = config.get<sol::optional<int>>("capitals")) {
                tts->setCapitals(*v);
            }

            ssb->setVoice(tts, repeat);

            manager_->addStimulus(name, ssb, "ssb", freq, amplitude);

            std::cout << "[Stimulus] Added SSB espeak voice '" << name << "': "
                      << freq / 1e6 << " MHz " << modeStr << std::endl;
            return;
        }

        // Check for audio file (WAV)
        sol::optional<std::string> audioFileOpt = config["audioFile"];
        if (audioFileOpt) {
            bool repeat = config.get_or("loop", true);
            uint32_t sampleRate = 0;
            auto samples = loadWavFile(*audioFileOpt, sampleRate);
            
            if (!samples.empty()) {
                ssb->setAudioSamples(std::move(samples), sampleRate, repeat);
                manager_->addStimulus(name, ssb, "ssb", freq, amplitude);
                std::cout << "[Stimulus] Added SSB audio file '" << name << "': "
                          << freq / 1e6 << " MHz " << modeStr << ", "
                          << *audioFileOpt << " (" << samples.size() << " samples @ "
                          << sampleRate << " Hz)" << std::endl;
            } else {
                std::cerr << "[Stimulus] FAILED to load WAV file for SSB '" << name << "': " << *audioFileOpt << std::endl;
            }
            return;
        }

        // Default: 1kHz tone
        ssb->setTones({1000.0});
        manager_->addStimulus(name, ssb, "ssb", freq, amplitude);

        std::cout << "[Stimulus] Added SSB '" << name << "': "
                  << freq / 1e6 << " MHz " << modeStr << ", default tone" << std::endl;
    };

    // stimulus.addAm(name, config)
    stimulus["addAm"] = [this](const std::string& name, sol::table config) {
        double freq = config.get_or("freq", 1.0e6);
        double amplitude = config.get_or("amplitude", 50e-6);
        double modIndex = config.get_or("modIndex", 0.8);

        auto am = std::make_shared<AMGenerator>(freq, amplitude);
        am->setModulationIndex(modIndex);

        // Check for tones
        sol::optional<sol::table> tonesOpt = config["tones"];
        if (tonesOpt) {
            std::vector<double> tones;
            for (auto& kv : *tonesOpt) {
                tones.push_back(kv.second.as<double>());
            }
            am->setTones(tones);
            manager_->addStimulus(name, am, "am", freq, amplitude);
            std::cout << "[Stimulus] Added AM '" << name << "': "
                      << freq / 1e6 << " MHz, " << tones.size() << " tone(s), "
                      << (int)(modIndex * 100) << "% mod" << std::endl;
            return;
        }

        // Check for audio file (WAV)
        sol::optional<std::string> audioFileOpt = config["audioFile"];
        if (audioFileOpt) {
            bool repeat = config.get_or("loop", true);
            uint32_t sampleRate = 0;
            auto samples = loadWavFile(*audioFileOpt, sampleRate);
            
            if (!samples.empty()) {
                am->setAudioSamples(std::move(samples), sampleRate, repeat);
                manager_->addStimulus(name, am, "am", freq, amplitude);
                std::cout << "[Stimulus] Added AM audio file '" << name << "': "
                          << freq / 1e6 << " MHz, " << *audioFileOpt 
                          << " (" << samples.size() << " samples @ "
                          << sampleRate << " Hz), " << (int)(modIndex * 100) << "% mod" << std::endl;
            } else {
                std::cerr << "[Stimulus] FAILED to load WAV file for AM '" << name << "': " << *audioFileOpt << std::endl;
            }
            return;
        }

        // Default: 1kHz tone
        am->setTones({1000.0});
        manager_->addStimulus(name, am, "am", freq, amplitude);
        std::cout << "[Stimulus] Added AM '" << name << "': "
                  << freq / 1e6 << " MHz, default tone, "
                  << (int)(modIndex * 100) << "% mod" << std::endl;
    };

    // stimulus.addRFCapture(name, config)
    stimulus["addRFCapture"] = [this](const std::string& name, sol::table config) {
        std::string path = config.get<std::string>("path");
        double freq = config.get_or("freq", 0.0);
        double amplitude = config.get_or("amplitude", 1.0);
        bool loop = config.get_or("loop", true);
        bool swapIQ = config.get_or("swapIQ", false);

        auto player = std::make_shared<RFCapturePlayer>();
        
        // Try to load as WAV
        if (player->loadWav(path)) {
            player->setCenterFrequency(freq);
            player->setAmplitude(amplitude);
            player->setLooping(loop);
            player->setSwapIQ(swapIQ);
            
            manager_->addStimulus(name, player, "rf-capture", freq, amplitude);
            
            std::cout << "[Stimulus] Added RFCapture '" << name << "': "
                      << path << " (" << player->getSampleCount() << " samples @ "
                      << player->getSampleRate() / 1e3 << " kHz)" << std::endl;
        } else {
            std::cerr << "[Stimulus] FAILED to load RFCapture file: " << path << std::endl;
        }
    };

    // stimulus.addTone(name, config)
    stimulus["addTone"] = [this](const std::string& name, sol::table config) {
        double freq = config.get_or("freq", 14.0e6);
        double amplitude = config.get_or("amplitude", 50e-6);

        auto tone = std::make_shared<ToneGenerator>(freq, amplitude);

        // Check for additional tones
        sol::optional<sol::table> tonesOpt = config["tones"];
        if (tonesOpt) {
            for (auto& kv : *tonesOpt) {
                sol::table t = kv.second.as<sol::table>();
                double f = t.get_or("freq", freq);
                double a = t.get_or("amplitude", amplitude);
                double p = t.get_or("phase", 0.0);
                tone->addTone(f, a, p);
            }
        }

        manager_->addStimulus(name, tone, "tone", freq, amplitude);

        std::cout << "[Stimulus] Added Tone '" << name << "': "
                  << freq / 1e6 << " MHz" << std::endl;
    };

    // stimulus.addSweep(name, config)
    // Frequency sweep for passband measurement
    stimulus["addSweep"] = [this](const std::string& name, sol::table config) {
        double startFreq = config.get_or("start", 1.0e6);   // Default 1 MHz
        double endFreq = config.get_or("end", 30.0e6);      // Default 30 MHz
        double amplitude = config.get_or("amplitude", 50e-6); // ~S9 default
        double rate = config.get_or("rate", 1.0e6);         // Default 1 MHz/s

        // Alternative: specify duration instead of rate
        sol::optional<double> durationOpt = config["duration"];
        if (durationOpt) {
            rate = std::abs(endFreq - startFreq) / *durationOpt;
        }

        auto sweep = std::make_shared<SweepGenerator>(startFreq, endFreq, amplitude, rate);

        // Sweep mode
        std::string modeStr = config.get_or<std::string>("mode", "linear");
        if (modeStr == "log" || modeStr == "logarithmic") {
            sweep->setSweepMode(SweepGenerator::SweepMode::Logarithmic);
        }

        // Repeat mode
        std::string repeatStr = config.get_or<std::string>("repeat", "repeat");
        if (repeatStr == "once" || repeatStr == "oneshot") {
            sweep->setRepeatMode(SweepGenerator::RepeatMode::OneShot);
        } else if (repeatStr == "pingpong" || repeatStr == "bounce") {
            sweep->setRepeatMode(SweepGenerator::RepeatMode::PingPong);
        } else {
            sweep->setRepeatMode(SweepGenerator::RepeatMode::Repeat);
        }

        manager_->addStimulus(name, sweep, "sweep", startFreq, amplitude);

        double duration = sweep->sweepDuration();
        std::cout << "[Stimulus] Added Sweep '" << name << "': "
                  << startFreq / 1e6 << "-" << endFreq / 1e6 << " MHz, "
                  << rate / 1e6 << " MHz/s (" << duration << "s sweep)"
                  << std::endl;
    };

    // stimulus.addNoise(name, config)
    stimulus["addNoise"] = [this](const std::string& name, sol::table config) {
        double rms = config.get_or("rms", 10e-6);  // 10µV default
        std::string type = config.get_or<std::string>("type", "thermal");

        std::shared_ptr<NoiseGenerator> noise;
        if (type == "thermal") {
            // Thermal noise at room temperature, 3kHz bandwidth
            noise = std::make_shared<NoiseGenerator>(
                NoiseGenerator::thermal(290.0, 3000.0));
            // Scale to requested RMS
            // double thermalRms = noise->getSample(0);  // Get baseline
            noise = std::make_shared<NoiseGenerator>(rms);
        } else {
            noise = std::make_shared<NoiseGenerator>(rms);
        }

        manager_->addStimulus(name, noise, "noise", 0.0, rms);

        std::cout << "[Stimulus] Added Noise '" << name << "': "
                  << rms * 1e6 << " µV RMS" << std::endl;
    };

    // stimulus.remove(name)
    stimulus["remove"] = [this](const std::string& name) {
        bool removed = manager_->removeStimulus(name);
        if (removed) {
            std::cout << "[Stimulus] Removed '" << name << "'" << std::endl;
        }
        return removed;
    };

    // stimulus.clear()
    stimulus["clear"] = [this]() {
        manager_->clearAll();
        std::cout << "[Stimulus] Cleared all stimuli" << std::endl;
    };

    // stimulus.enable(name, enabled)
    stimulus["enable"] = [this](const std::string& name, bool enabled) {
        manager_->setEnabled(name, enabled);
    };

    // stimulus.list() -> table of {name -> {type, freq, amplitude, active}}
    stimulus["list"] = [this](sol::this_state s) {
        sol::state_view lua(s);
        sol::table result = lua.create_table();

        for (const auto& info : manager_->listInfo()) {
            sol::table entry = lua.create_table();
            entry["type"] = info.type;
            entry["freq"] = info.frequencyHz;
            entry["amplitude"] = info.amplitudeV;
            entry["active"] = info.active;
            result[info.name] = entry;
        }

        return result;
    };

    // stimulus.count() -> number
    stimulus["count"] = [this]() {
        return manager_->count();
    };

    std::cout << "[Stimulus] Lua bindings registered" << std::endl;
}

bool StimulusLua::loadScript(sol::state& lua, const std::string& path) {
    std::ifstream file(path);
    if (!file.is_open()) {
        std::cerr << "[Stimulus] Failed to open script: " << path << std::endl;
        return false;
    }

    try {
        sol::protected_function_result result = lua.safe_script_file(path);
        if (!result.valid()) {
            sol::error err = result;
            std::cerr << "[Stimulus] Script error: " << err.what() << std::endl;
            return false;
        }
        std::cout << "[Stimulus] Loaded script: " << path << std::endl;
        return true;
    } catch (const std::exception& e) {
        std::cerr << "[Stimulus] Script exception: " << e.what() << std::endl;
        return false;
    }
}

} // namespace nexrx
