alanmimms/NexRx/app/src/TwinConn.hpp

#pragma once

#include "TCPControlClient.hpp"
#include "UDPStreamClient.hpp"
#include "transport/IQFrame.hpp"
#include "Control.hpp"

#include <atomic>
#include <functional>
#include <memory>
#include <string>
#include <thread>
#include <vector>
#include <mutex>

namespace nexrx {

struct TwinConfig {
  std::string host = "127.0.0.1";
  uint16_t controlPort = 5000;
  uint16_t streamPort = 5001;
  size_t frameBufferSize = 1024;
  size_t receiveBufferSize = 65536;
  bool verbose = false;
};

class TwinConn {
public:
  using FrameCallback = std::function<void(const IQFrame&)>;
  using BatchCallback = std::function<void(const std::vector<IQFrame>&)>;

  TwinConn() = default;
  ~TwinConn();

  TwinConn(const TwinConn&) = delete;
  TwinConn& operator=(const TwinConn&) = delete;

  bool initialize(const TwinConfig& cfg = TwinConfig{});
  void shutdown();

  [[nodiscard]] bool isConnected() const { return connected; }

  void setFrameCallback(FrameCallback callback) {
    std::lock_guard<std::mutex> lock(callbackMutex);
    frameCallback = std::move(callback);
  }

  void setBatchCallback(BatchCallback callback) {
    std::lock_guard<std::mutex> lock(callbackMutex);
    batchCallback = std::move(callback);
  }

  bool startReceiving();
  void stopReceiving();

  [[nodiscard]] bool isReceiving() const { return receiving; }
  size_t pollFrames(size_t maxFrames = 100);

  /* Control Commands */
  bool setVFO(double freqHz, double offsetHz);
  bool setAtten(int dbValue);
  bool setPGAGain(int code);
  bool setAGCMode(int mode);
  bool setISGFreq(double freqHz);
  bool setISGEnable(bool enabled);
  bool setHpfBypass(bool bypass);
  bool setBpfIndex(int index);
  bool setTrMode(int mode);
  bool setOSDOffsetKHz(double khz);
  bool setQsdOffsetKHz(double khz);
  bool startStream();
  bool stopStream();
  uint64_t getTimestamp();
  std::vector<uint8_t> getState();
  void pollStateAsync(); // Called by background thread
  bool sendCalibrationStimulus(double freqHz, uint64_t durationMs);

  struct VersionInfo {
    uint32_t magic = 0;
    uint16_t major = 0;
    uint16_t minor = 0;
    uint16_t patch = 0;
    uint32_t hwState = 0;
    bool valid = false;
    bool compatible = false;
  };

  VersionInfo checkFirmwareVersion();
  bool loadCPLDBitstream(const std::vector<uint8_t>& bitstream);

  std::vector<uint8_t> sendCBORRequest(uint32_t cmdId, const std::vector<uint8_t>& argsCBOR);

  [[nodiscard]] uint64_t getFramesReceived() const { return framesReceivedCount; }
  [[nodiscard]] uint64_t getPacketsReceived() const;
  [[nodiscard]] uint64_t getLastSequence() const { return lastSequenceReceived; }
  [[nodiscard]] uint64_t getBufferOverruns() const;
  [[nodiscard]] uint64_t getFramesDropped() const;

private:
  void receiveLoop();
  std::vector<uint8_t> processResponse(const std::vector<uint8_t>& responseData, uint32_t cmdId);

  TwinConfig config;
  std::unique_ptr<TCPControlClient> control;
  std::mutex controlMutex; // Protect TCP control connection

  std::unique_ptr<UDPStreamClient> stream;
  bool connected = false;

  mutable std::mutex callbackMutex;
  FrameCallback frameCallback;
  BatchCallback batchCallback;

  std::vector<uint8_t> cachedStateCBOR;
  std::mutex stateMutex; // Protect state cache

  std::thread receiveThread;
  std::atomic<bool> receiving{false};
  std::atomic<bool> stopRequested{false};

  std::atomic<uint64_t> framesReceivedCount{0};
  std::atomic<uint64_t> lastSequenceReceived{0};

  IQFrame lastFrameReceived{};
  std::vector<IQFrame> frameBuffer;
};

} // namespace nexrx
