alanmimms/NexRx/app/src/UDPStreamClient.cpp

#include "UDPStreamClient.hpp"
#include <cstring>
#include <iostream>

namespace nexrx {

using namespace nexrx::net;

UDPStreamClient::UDPStreamClient(const UDPStreamClientConfig& cfg)
  : config(cfg) {
  receiveBuffer.resize(cfg.receiveBufferSize);
}

UDPStreamClient::~UDPStreamClient() {
  disconnect();
}

bool UDPStreamClient::connect() {
  socket = ::socket(AF_INET, SOCK_DGRAM, 0);
  if (socket == SOCKET_INVALID) {
    std::cerr << "[UDPClient] Failed to create socket" << std::endl;
    return false;
  }
  
  struct timeval tv{};
  tv.tv_sec = 0;
  tv.tv_usec = 100000;
  ::setsockopt(socket, SOL_SOCKET, SO_RCVTIMEO, &tv, sizeof(tv));

  int rcvbuf = 2 * 1024 * 1024;
  ::setsockopt(socket, SOL_SOCKET, SO_RCVBUF, &rcvbuf, sizeof(rcvbuf));

  sockaddr_in addr{};
  addr.sin_family = AF_INET;
  addr.sin_port = htons(config.port);
  addr.sin_addr.s_addr = INADDR_ANY;
  
  if (::bind(socket, (struct sockaddr*)&addr, sizeof(addr)) < 0) {
    std::cerr << "[UDPClient] Failed to bind to port " << config.port << " errno=" << errno << std::endl;
    socket_close(socket);
    socket = SOCKET_INVALID;
    return false;
  }

  std::cout << "[UDPClient] Bound to port " << config.port << ", starting receive thread" << std::endl;
  running = true;
  receiveThread = std::thread(&UDPStreamClient::receiveLoop, this);
  return true;
}

void UDPStreamClient::disconnect() {
  running = false;
  if (socket != SOCKET_INVALID) {
    ::shutdown(socket, SHUT_RDWR);
    socket_close(socket);
    socket = SOCKET_INVALID;
  }
  if (receiveThread.joinable()) {
    receiveThread.join();
  }
}

bool UDPStreamClient::isConnected() const {
  return socket != SOCKET_INVALID;
}

std::string UDPStreamClient::name() const {
  return "UDP Client";
}

TransportError UDPStreamClient::writeBatch(std::span<const IQFrame>) {
  return TransportError::Other;
}

TransportError UDPStreamClient::write(const IQFrame&) {
  return TransportError::Other;
}

void UDPStreamClient::receiveLoop() {
  uint8_t buffer[65536];
  bool firstLog = true;
  while (running) {
    int len = ::recv(socket, reinterpret_cast<char*>(buffer), sizeof(buffer), 0);
    if (len < 0) {
      continue;
    }
    if (len < static_cast<int>(sizeof(IQPacketHeader))) {
      continue;
    }

    const IQPacketHeader* header = reinterpret_cast<const IQPacketHeader*>(buffer);
    if (header->magic != IQPacketHeader::MAGIC || header->version != 2) {
      continue;
    }

    if (firstLog) {
      firstLog = false;
    }

    size_t framesInPacket = header->frameCount;
    if (!firstFrame.load()) {
      uint32_t expectedSeq = lastSequence.load() + 1;
      if (header->sequence > expectedSeq) {
        uint32_t lostPkts = header->sequence - expectedSeq;
        framesDroppedCount += static_cast<uint64_t>(lostPkts) * framesInPacket;
      }
    } else {
      firstFrame.store(false);
    }
    lastSequence.store(header->sequence);

    const int32_t* samples = reinterpret_cast<const int32_t*>(buffer + sizeof(IQPacketHeader));

    for (size_t i = 0; i < framesInPacket; i++) {
      IQFrame frame;
      frame.sequence = header->sequence;
      frame.timestampNS = header->timestampNS;
      frame.sample.i = samples[i*2 + 0];
      frame.sample.q = samples[i*2 + 1];

      size_t nextWrite = (writePos.load() + 1) % config.receiveBufferSize;
      if (nextWrite == readPos.load()) {
        bufferOverrunsCount++;
      } else {
        receiveBuffer[writePos.load()] = frame;
        writePos.store(nextWrite);
        framesReceivedCount++;
      }
    }
    packetsReceivedCount++;
  }
}

Result<IQFrame> UDPStreamClient::read(std::chrono::milliseconds timeout) {
  (void)timeout;
  size_t r = readPos.load();
  size_t w = writePos.load();
  if (r == w) {
    return {{}, TransportError::Timeout};
  }
  IQFrame frame = receiveBuffer[r];
  readPos.store((r + 1) % config.receiveBufferSize);
  return {frame, TransportError::None};
}

Result<std::vector<IQFrame>> UDPStreamClient::readBatch(size_t maxFrames, std::chrono::milliseconds timeout) {
  (void)timeout;
  std::vector<IQFrame> batch;
  while (batch.size() < maxFrames) {
    auto res = read(std::chrono::milliseconds(0));
    if (!res.ok()) {
      break;
    }
    batch.push_back(res.value);
  }
  if (batch.empty()) {
    return {{}, TransportError::Timeout};
  }
  return {batch, TransportError::None};
}

size_t UDPStreamClient::available() const {
  size_t w = writePos.load();
  size_t r = readPos.load();
  if (w >= r) {
    return w - r;
  }
  return config.receiveBufferSize - (r - w);
}

size_t UDPStreamClient::capacity() const {
  return config.receiveBufferSize;
}

void UDPStreamClient::clear() {
  readPos.store(writePos.load());
}

} // namespace nexrx
