alanmimms/NexRx/twin/src/sampler/ADCSampler.hpp

// NexRx Digital Twin - ADC Sampler
//
// Samples Xyce I/Q output nodes at 384ksps ADC rate.
// Converts analog voltages to 24-bit signed digital values.
//
// Copyright 2026 NexRx Project - MIT License

#pragma once

#include "transport/IQFrame.hpp"
#include "xyce/XyceWrapper.hpp"

#include <array>
#include <cstdint>
#include <functional>
#include <optional>
#include <string>

namespace nexrx {

//======================================================================
// ADC Configuration
//======================================================================
struct ADCConfig {
  // Sample rate
  static constexpr double SAMPLE_RATE_HZ = 384000.0;
  static constexpr double SAMPLE_PERIOD_S = 1.0 / SAMPLE_RATE_HZ;
  static constexpr uint64_t SAMPLE_PERIOD_NS = 2604;  // 1e9 / 384000

  // ADC specifications (matching real hardware)
  static constexpr double VREF = 3.3;                   // ADC reference voltage
  static constexpr double VCM = 1.65;                   // Common-mode voltage (mid-rail)
  static constexpr double FULL_SCALE = 1.65;            // +/- 1.65V around VCM
  static constexpr int32_t ADC_MAX = 8388607;           // 2^23 - 1 (24-bit signed)
  static constexpr int32_t ADC_MIN = -8388608;          // -2^23

  // Node names in the netlist for I/Q outputs
  std::array<std::string, 2> iNodes = {"O0_I", "O1_I"};
  std::array<std::string, 2> qNodes = {"O0_Q", "O1_Q"};
};

//======================================================================
// ADC Sampler
//
// Samples the 4 I/Q channels from Xyce at 384ksps rate.
// Maintains sample timing and sequence numbering.
//
// Usage:
//   ADCSampler sampler(xyceWrapper, config);
//   while (running) {
//       xyce.stepTo(sampler.getNextSampleTime());
//       if (auto frame = sampler.sample()) {
//           transport.write(*frame);
//       }
//   }
//======================================================================
class ADCSampler {
public:
  using FrameCallback = std::function<void(const IQFrame&)>;

  explicit ADCSampler(XyceWrapper& xyce, const ADCConfig& config = {});

  // Get the time of the next sample in seconds
  [[nodiscard]] double getNextSampleTime() const;

  // Get the time of the next sample in nanoseconds
  [[nodiscard]] uint64_t getNextSampleTimeNS() const;

  // Check if current Xyce time is at or past next sample time
  [[nodiscard]] bool isSampleDue() const;

  // Take a sample from Xyce, returns frame if successful
  std::optional<IQFrame> sample();

  // Take a sample and invoke callback
  bool sampleWithCallback(const FrameCallback& callback);

  // Reset sampler state (e.g., for new simulation)
  void reset();

  // Get current sample count
  [[nodiscard]] uint64_t getSampleCount() const { return sampleCount; }

  // Get current sequence number (wraps at 2^32)
  [[nodiscard]] uint32_t getSequence() const { return sequence; }

  // Statistics
  [[nodiscard]] uint64_t getMissedSamples() const { return missedSamples; }
  [[nodiscard]] uint64_t getErrorCount() const { return errorCount; }

private:
  // Convert voltage to 24-bit ADC value
  static int32_t voltageToADC(double voltage, double vcm = ADCConfig::VCM);

  // Sample a single I/Q pair
  std::optional<IQSample> sampleChannel(size_t channelIndex);

  XyceWrapper& xyce;
  ADCConfig config;

  uint64_t nextSampleTimeNS = 0;
  uint64_t sampleCount = 0;
  uint32_t sequence = 0;

  // Error tracking
  uint64_t missedSamples = 0;
  uint64_t errorCount = 0;
};

} // namespace nexrx
