alanmimms/NexRx/app/src/AudioEngine.cpp

/**
 * @file AudioEngine.cpp
 * @brief Audio playback engine implementation
 */

#define MINIAUDIO_IMPLEMENTATION
#include "miniaudio/miniaudio.h"

#include "AudioEngine.hpp"

#include <iostream>
#include <cmath>
#include <algorithm>

AudioEngine::AudioEngine() = default;

AudioEngine::~AudioEngine() {
  shutdown();
}

bool AudioEngine::init(uint32_t sampleRateIn, uint32_t channelsIn) {
  if (initialized) {
    return true;
  }

  sampleRate = sampleRateIn;
  channels = channelsIn;

  device = new ma_device();

  ma_device_config config = ma_device_config_init(ma_device_type_playback);
  config.playback.format = ma_format_f32;
  config.playback.channels = channels;
  config.sampleRate = sampleRate;
  config.dataCallback = &AudioEngine::dataCallback;
  config.pUserData = this;

  // Reduce period size for lower latency
  config.periodSizeInMilliseconds = 10; 
  config.periods = 2;
ma_result result = ma_device_init(nullptr, &config, device);
  if (result != MA_SUCCESS) {
    std::cerr << "[AudioEngine] Failed to initialize audio device: " << result << std::endl;
    delete device;
    device = nullptr;
    return false;
  }

  initialized = true;

  // Pre-allocate callback buffer
  callbackBuffer.resize(8192 * channels, 0.0f);

  return true;
}

void AudioEngine::shutdown() {
  if (!initialized) {
    return;
  }

  stop();

  if (device) {
    ma_device_uninit(device);
    delete device;
    device = nullptr;
  }

  initialized = false;
}

bool AudioEngine::start() {
  if (!initialized) {
    std::cerr << "[AudioEngine] Cannot start: not initialized" << std::endl;
    return false;
  }
  if (playing.load()) return true;

  ma_result result = ma_device_start(device);
  if (result != MA_SUCCESS) {
    std::cerr << "[AudioEngine] Failed to start audio device: " << result << std::endl;
    return false;
  }

  playing.store(true);
  return true;
}

void AudioEngine::stop() {
  if (!initialized || !playing.load()) {
    return;
  }

  ma_device_stop(device);
  playing.store(false);
}

void AudioEngine::setVolume(float vol) {
  volume.store(std::clamp(vol, 0.0f, 2.0f));
}

void AudioEngine::setTestTone(bool enabled, float frequency) {
  testToneEnabled.store(enabled);
  testToneFrequency.store(frequency);
  if (!enabled) {
    testTonePhase = 0.0f;
  }
}

void AudioEngine::dataCallback(ma_device* dev, void* output, const void* /*input*/, uint32_t frameCount) {
  AudioEngine* engine = static_cast<AudioEngine*>(dev->pUserData);
  engine->processAudio(static_cast<float*>(output), frameCount);
}
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
